SmallPond/X-Knob/1.Firmware/src/app/Pages/SurfaceDial/SurfaceDialModel.cpp

#include "SurfaceDialModel.h"
#include "app/Accounts/Account_Master.h"
#include <Arduino.h>
#include "hal/motor.h"
#include "hal/hal.h"

using namespace Page;

SurfaceDialModel::SurfaceDialModel()
{
    app = APP_MODE_SUPER_DIAL;
}

void SurfaceDialModel::GetKnobStatus(SurfaceDialInfo *info)
{
    PlaygroundModel::GetKnobStatus(info);
	info->is_ble_connected = HAL::surface_dial_is_connected();
}

void SurfaceDialModel::SetPlaygroundMode(int16_t mode)
{
	PlaygroundModel::SetPlaygroundMode(mode);
}


void SurfaceDialModel::Init()
{
    PlaygroundModel::Init();
}

void SurfaceDialModel::Deinit()
{
	PlaygroundModel::Deinit();
}
void SurfaceDialModel::ChangeMotorMode(int mode)
{
	PlaygroundModel::ChangeMotorMode(mode);
}
