SmallPond/X-Knob/1.Firmware/src/app/Pages/SurfaceDial/SurfaceDialModel.h

#ifndef __SURFACE_DIAL_MODEL_H
#define __SURFACE_DIAL_MODEL_H
#include "app/Utils/AccountSystem/Account.h"
#include "lvgl.h"
#include "../Playground/PlaygroundView.h"
#include "../Playground/PlaygroundModel.h"

typedef struct SurfaceDialInfo : PlaygroundInfo
{
	bool is_ble_connected;
} SurfaceDialInfo;

namespace Page
{

	class SurfaceDialModel : public PlaygroundModel
	{
	 public:
		SurfaceDialModel();
		void Init();
		void Deinit();
		void Update(void* pg_ui);
		void GetKnobStatus(SurfaceDialInfo* info);
		void ChangeMotorMode(int mode);
		void SetPlaygroundMode(int16_t mode);

		void onEvent(Account* account, Account::EventParam_t* param);
	 private:

	};

}

#endif
