SmallPond/X-Knob/1.Firmware/src/app/Pages/SurfaceDial/SurfaceDialView.h

#ifndef __SUPER_DIAL_VIEW_H
#define __SUPER_DIAL_VIEW_H
#include <Arduino.h>
#include "app/app.h"
#include "app/Pages/Page.h"
#include "../Playground/PlaygroundView.h"
#include "SurfaceDialModel.h"

namespace Page
{

class SurfaceDialView: public PlaygroundView
{
public:
    SurfaceDialView(){}
    void Create(lv_obj_t* root);
    void Delete();
    void UpdateView(SurfaceDialInfo *info);
    void SetPlaygroundMode(int16_t mode);


public:
    struct {
        lv_obj_t* img_super_dial;
    }m_ui;

private:
};

}

#endif // !__VIEW_H
