SmallPond/X-Knob/1.Firmware/src/hal/super_dial.cpp

#include "hal/hal.h"
#include "BleKeyboard.h"

BleKeyboard bleKeyboard("Surface Dial(Like)");



void HAL::super_dial_init(void)
{
    bleKeyboard.begin();
}

bool HAL::super_dial_is_connected(void)
{
    return bleKeyboard.isConnected();
}

void HAL::suer_dial_press(void)
{
    bleKeyboard.sendDialReport(DIAL_PRESS);
}

void HAL::suer_dial_release(void)
{
    bleKeyboard.sendDialReport(DIAL_RELEASE);
}


void HAL::super_dial_update(SuperDialMotion direction)
{
    if (bleKeyboard.isConnected()) {

        switch (direction)
        {
        case SUPER_DIAL_LEFT:
            bleKeyboard.sendDialReport(DIAL_L);
            break;
        case SUPER_DIAL_RIGHT:
            bleKeyboard.sendDialReport(DIAL_R);
            break;
        default:
            Serial.println("SuperDial: Error direction parameter");
            break;
        }
    }
}
